Its-Nevmo/92Mohr/20200912_191356.jpg

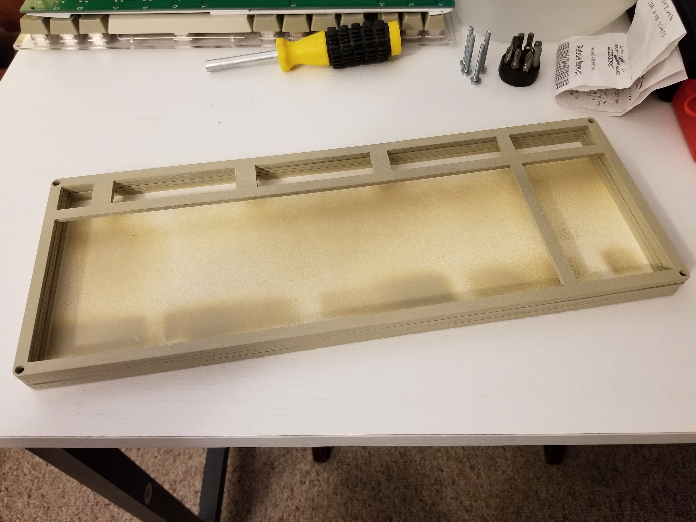
20200912_191356.jpg
