Its-Nevmo/92Mohr/20220419_164756.jpg

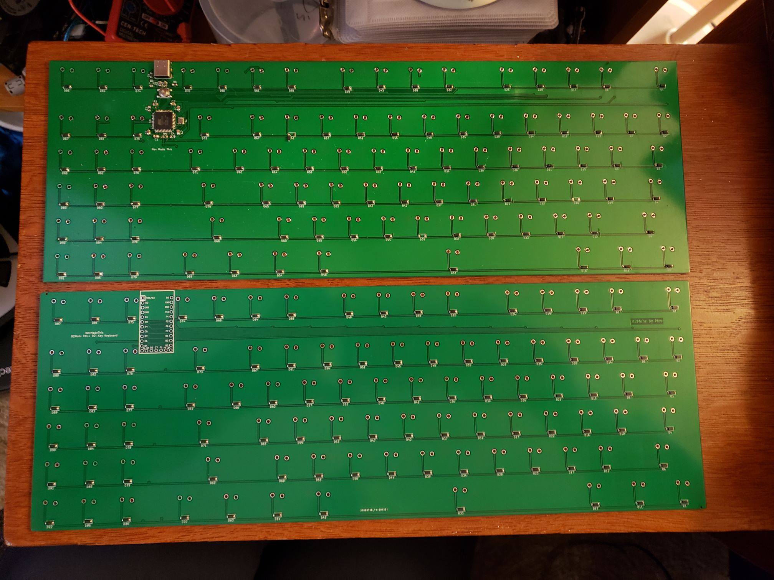
20220419_164756.jpg
